poulet-lab/Bpod_Stepper/PCB/bpod_stepper_1.3.1.brd

## EAGLE design PCB/bpod_stepper_1.3.1.brd (2021-09-14)

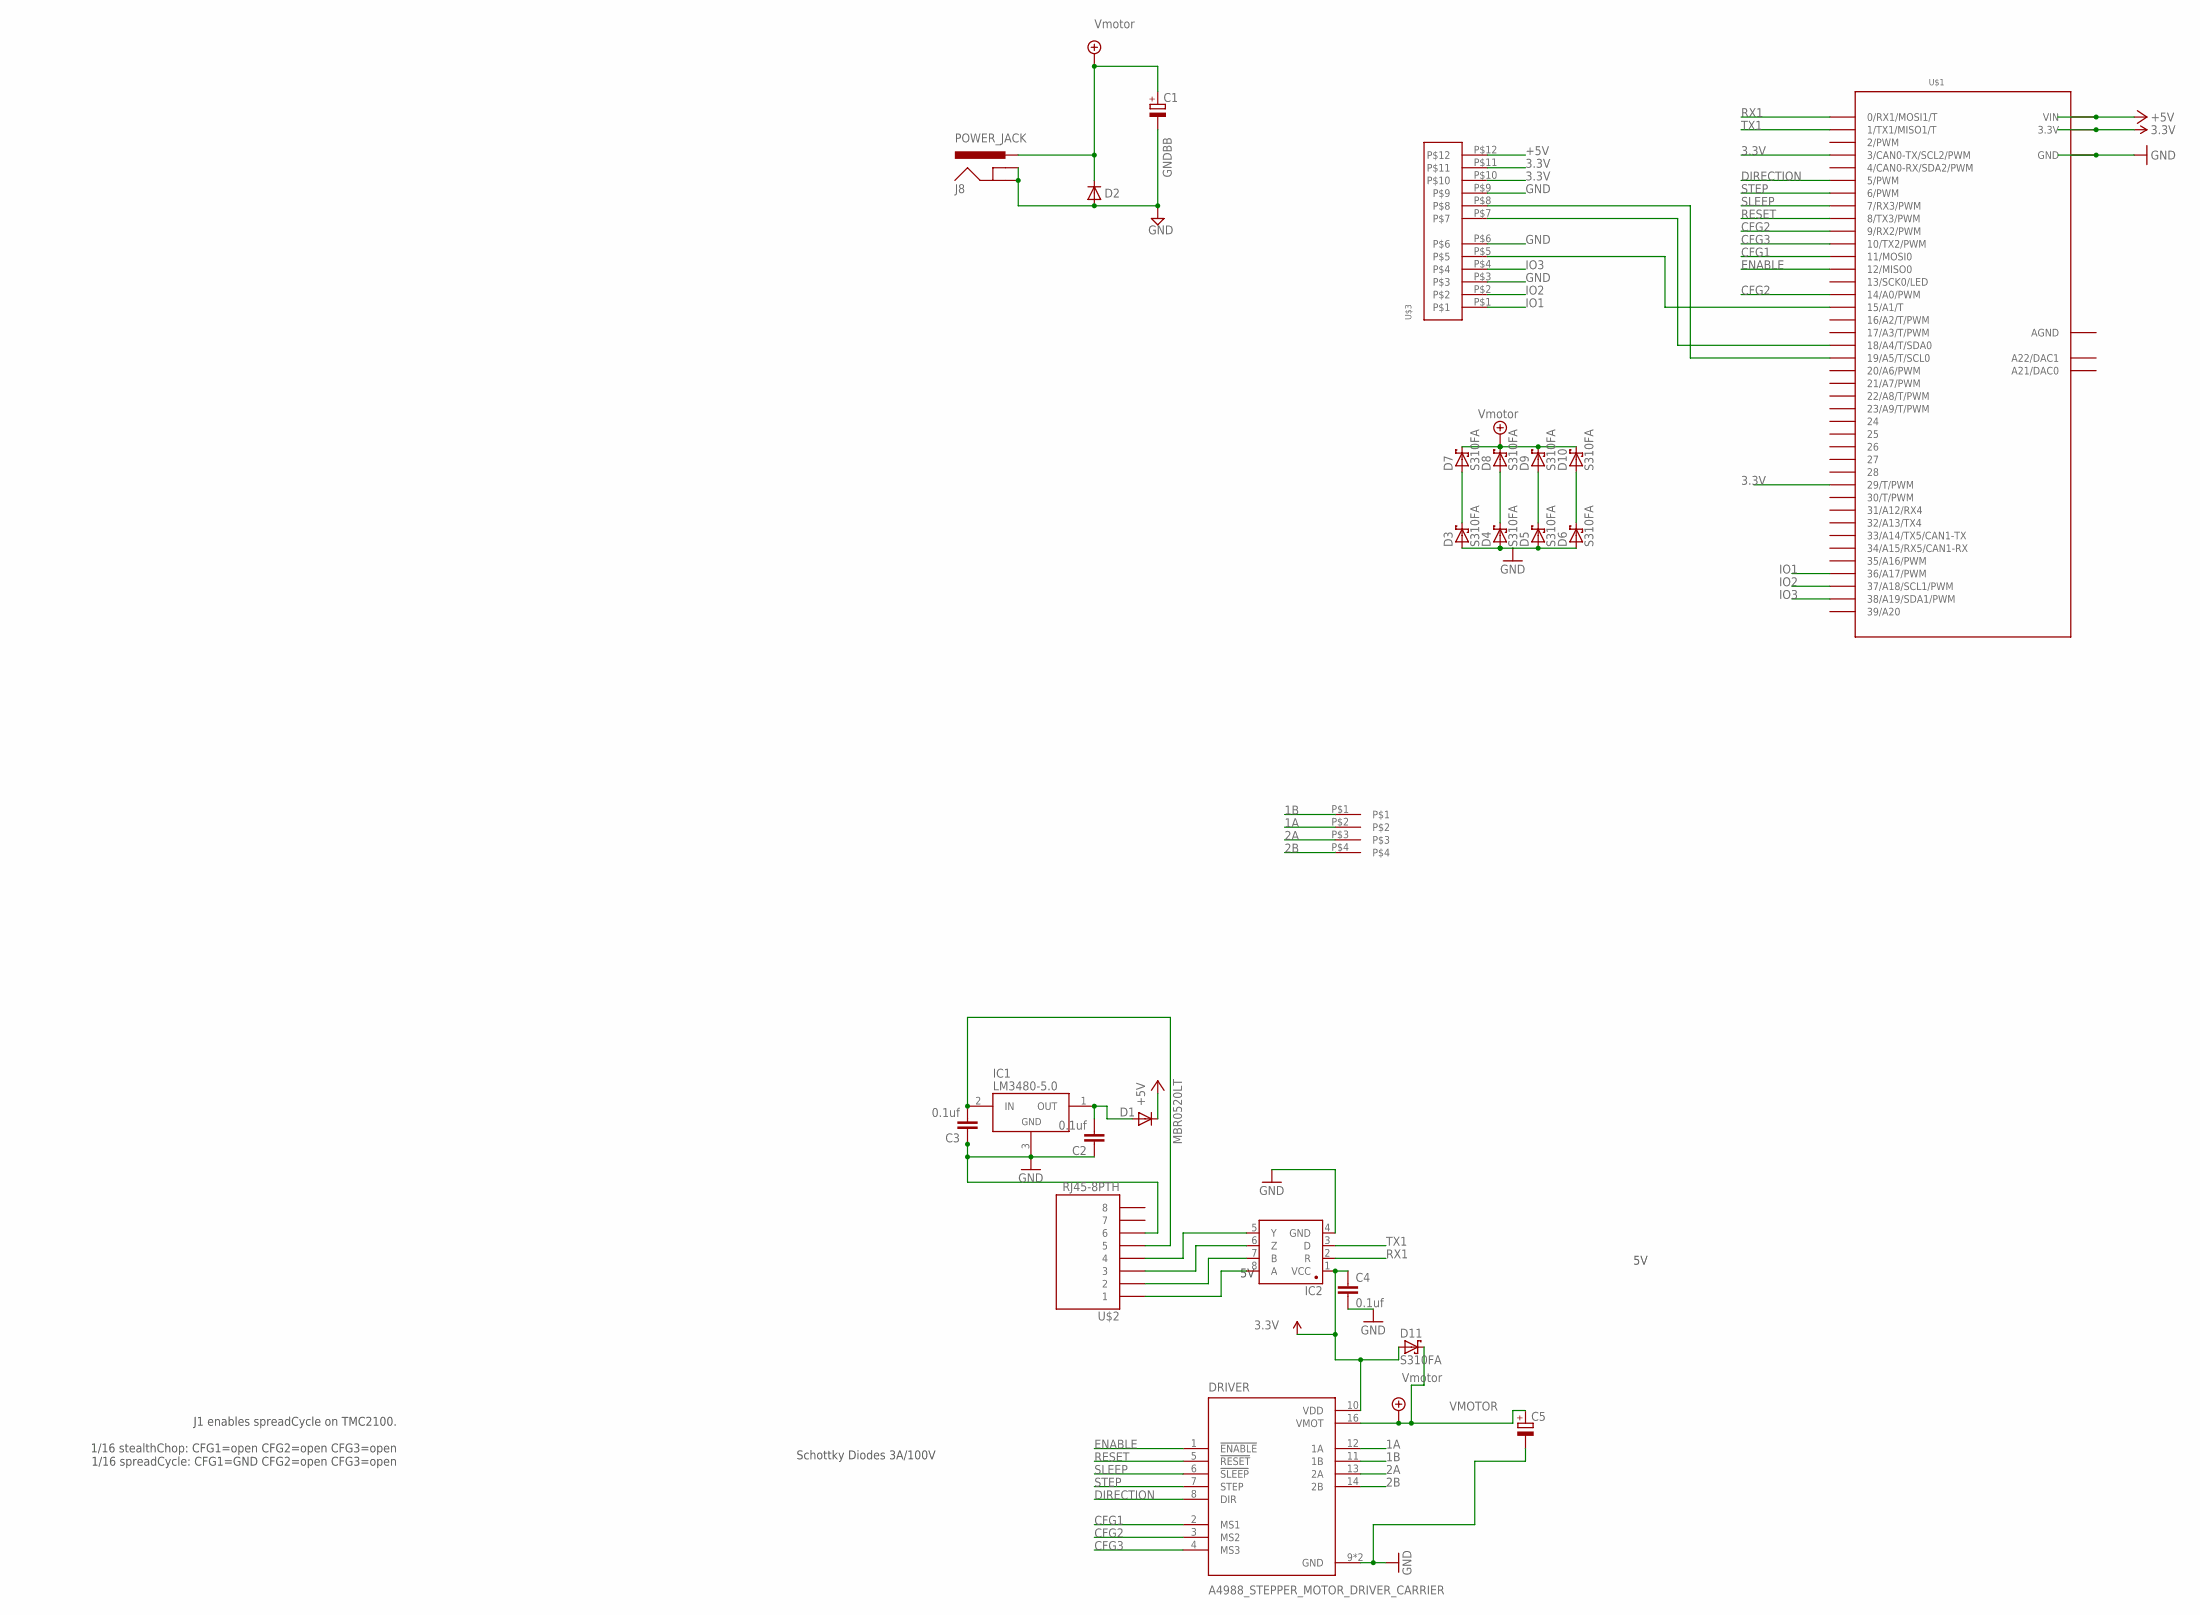
[picture p7: schematic bpod_stepper_1.3.1.sch]

Parts:
C1, C5: CPOL-EUG; PANASONIC_G
C2, C3, C4: 0.1uf; 1206@1
D1: MBR0520LT; SOD123
D2: DIODE-DO214AA; DO214AA
D3, D4, D5, D6, D7, D8, D9, D10, D11: S310FA; SOD123
DRIVER: A4988_STEPPER_MOTOR_DRIVER_CARRIER; MODULE_A4988_STEPPER_MOTOR_DRIVER_CARRIER
IC1: LM3480-5.0; SOT-23-3
IC2: SN65HVD31DR; SO08
J8: POWER_JACK; POWER_JACK_PTH
U$1: TEENSY_3.6_DIL
U$2: RJ45-8PTH; RJ45-8
U$3: 12POS_MOLEX_SOCKET
U$4: MOLEX395221004

Connections:
1A: D4.C, D8.A, DRIVER.12 (1A), U$4.P$2
1B: D3.C, D7.A, DRIVER.11 (1B), U$4.P$1
2A: D6.C, D10.A, DRIVER.13 (2A), U$4.P$3
2B: D5.C, D9.A, DRIVER.14 (2B), U$4.P$4
3.3V: C4.1, D11.A, DRIVER.10 (VDD), IC2.1 (VCC), U$1.3 (3/CAN0-TX/SCL2/PWM), U$1.3.3V, U$1.3.3V3 (3.3V), U$1.29 (29/T/PWM), U$3.P$10, U$3.P$11
+5V: D1.C, U$1.VIN, U$3.P$12
AGND: U$1.AGND
CFG1: DRIVER.2 (MS1), U$1.11 (11/MOSI0)
CFG2: DRIVER.3 (MS2), U$1.9 (9/RX2/PWM), U$1.14/A0 (14/A0/PWM)
CFG3: DRIVER.4 (MS3), U$1.10 (10/TX2/PWM)
DIRECTION: DRIVER.8 (DIR), U$1.5 (5/PWM)
ENABLE: DRIVER.1 (!ENABLE), U$1.12 (12/MISO0)
GND: C1.-, C2.1, C3.1, C4.2, C5.-, D2.A, D3.A, D4.A, D5.A, D6.A, DRIVER.9 (GND), DRIVER.15 (GND), IC1.3 (GND), IC2.4 (GND), J8.GND, J8.GNDBREAK, U$1.GND, U$1.GND1 (GND), U$2.6, U$3.P$3, U$3.P$6, U$3.P$9
IO1: U$1.36/A17 (36/A17/PWM), U$3.P$1
IO2: U$1.37/A18 (37/A18/SCL1/PWM), U$3.P$2
IO3: U$1.38/A19 (38/A19/SDA1/PWM), U$3.P$4
unnamed: U$1.19/A5 (19/A5/T/SCL0), U$3.P$8
unnamed: U$1.18/A4 (18/A4/T/SDA0), U$3.P$7
unnamed: U$1.15/A1 (15/A1/T), U$3.P$5
unnamed: IC2.8 (A), U$2.1
unnamed: IC2.7 (B), U$2.2
unnamed: IC2.6 (Z), U$2.3
unnamed: IC2.5 (Y), U$2.4
unnamed: C2.2, D1.A, IC1.1 (OUT)
unnamed: C3.2, IC1.2 (IN), U$2.5
RESET: DRIVER.5 (!RESET), U$1.8 (8/TX3/PWM)
RX1: IC2.2 (R), U$1.0 (0/RX1/MOSI1/T)
SLEEP: DRIVER.6 (!SLEEP), U$1.7 (7/RX3/PWM)
STEP: DRIVER.7 (STEP), U$1.6 (6/PWM)
TX1: IC2.3 (D), U$1.1 (1/TX1/MISO1/T)
VMOTOR: C1.+, C5.+, D2.C, D7.C, D8.C, D9.C, D10.C, D11.C, DRIVER.16 (VMOT), J8.PWR

Notes on the sheet:
GNDBB
Schottky Diodes 3A/100V
J1 enables spreadCycle on TMC2100. 1/16 stealthChop: CFG1=open CFG2=open CFG3=open 1/16 spreadCycle: CFG1=GND CFG2=open CFG3=open

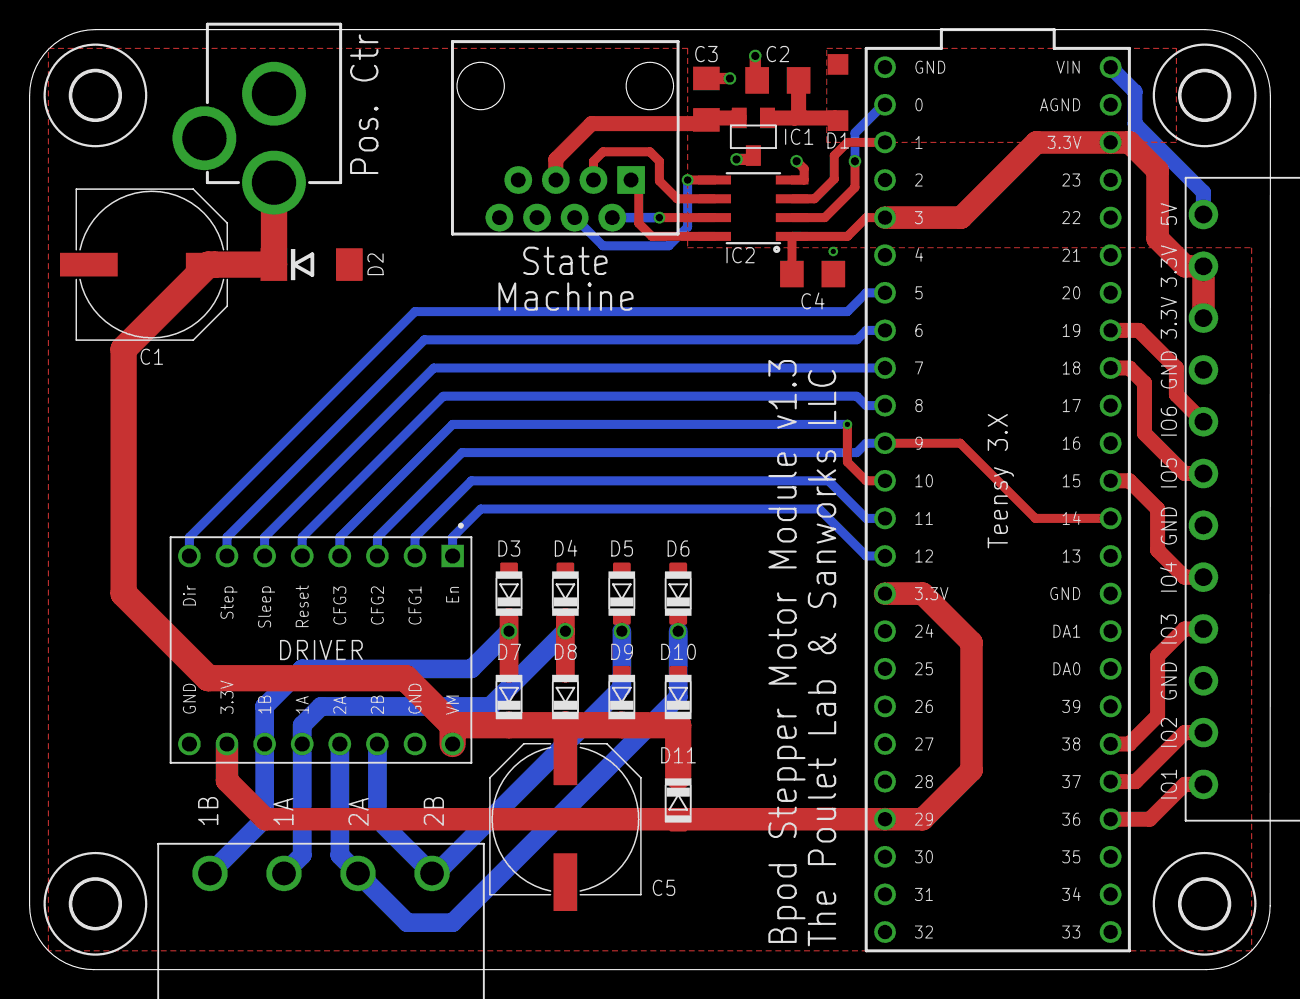
[picture p8: board bpod_stepper_1.3.1.brd from above]

Board: 2 copper layers, 83.8 x 63.5 mm, 28 parts (0 on the bottom side), 30 nets.

Other parts of the board:
U$7, U$8, U$9, U$10: 3,2
