poulet-lab/Bpod_Stepper/PCB/bpod_stepper_1.0.brd

## EAGLE design PCB/bpod_stepper_1.0.brd (2020-08-25)

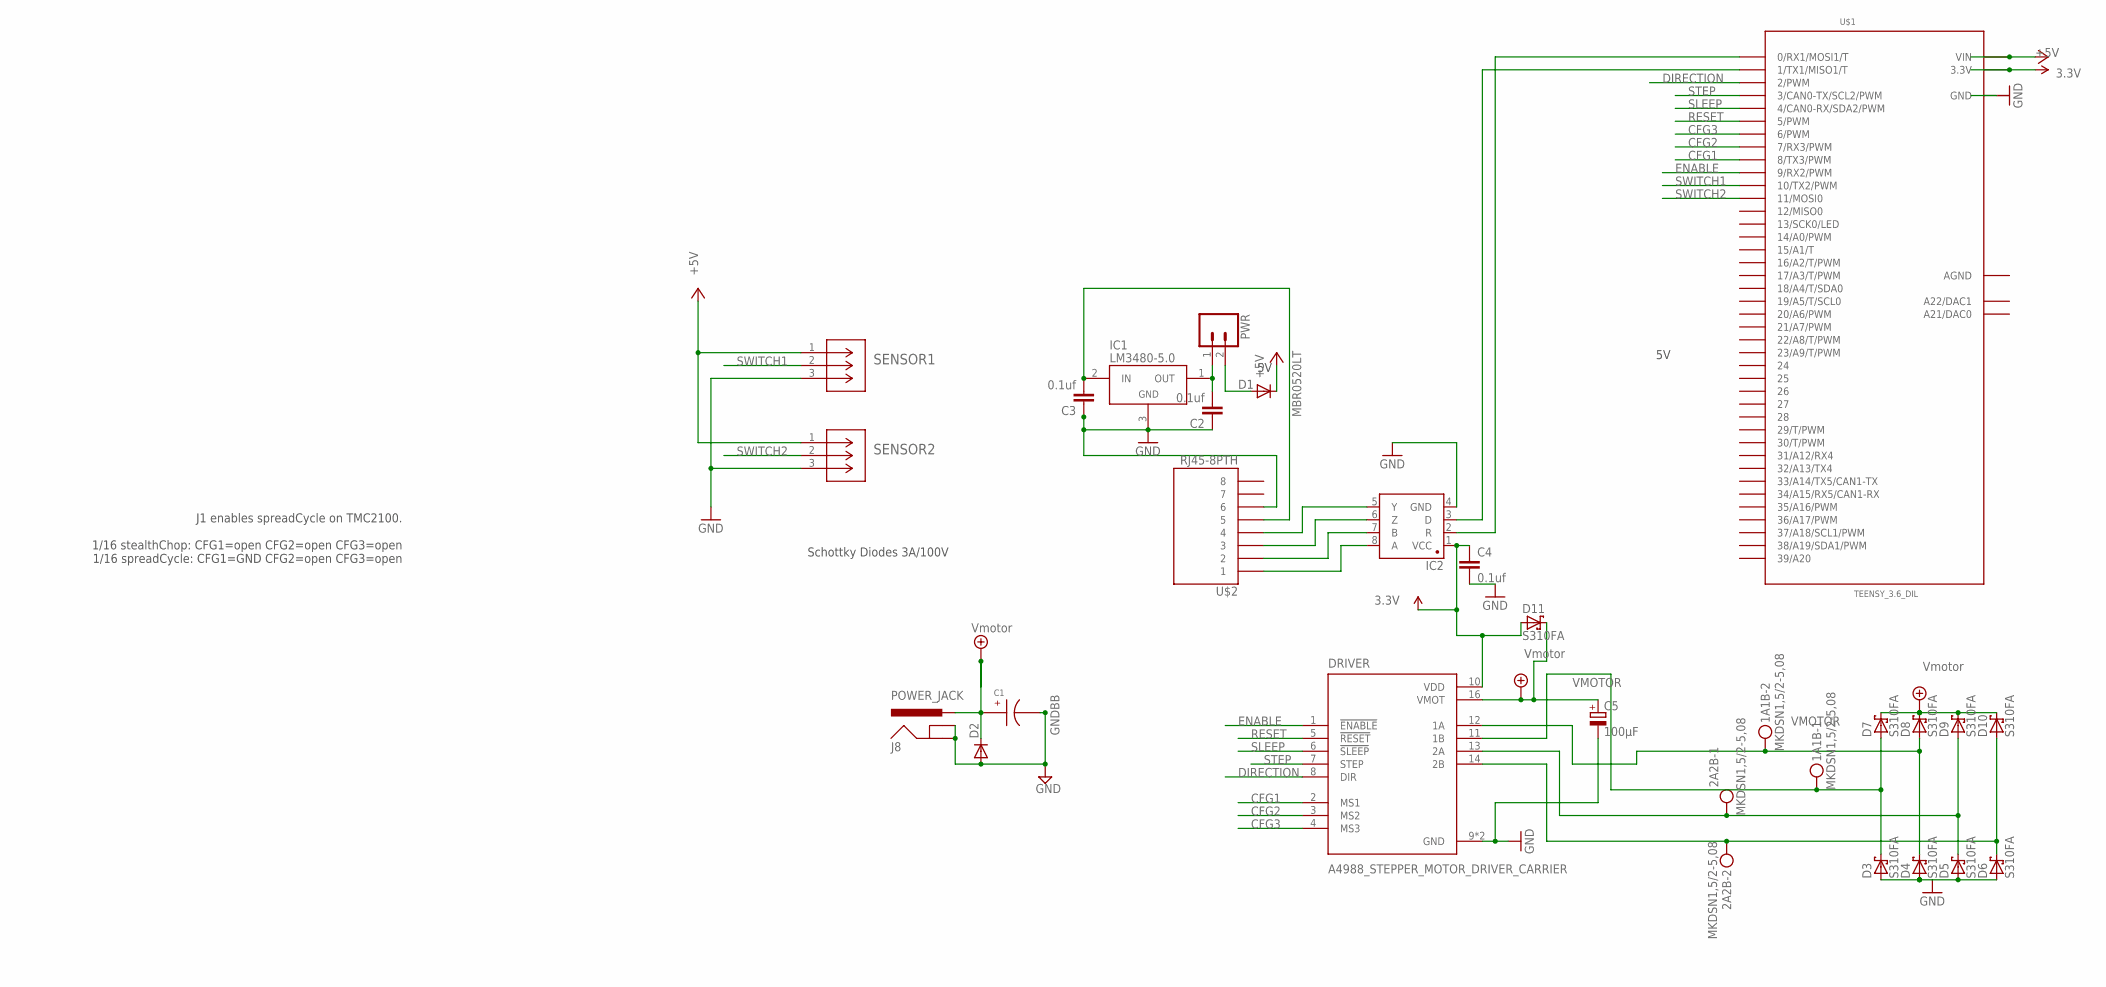
[picture p9: schematic bpod_stepper_1.0.sch]

Parts:
1A1B, 2A2B: MKDSN1,5/2-5,08
C1: EEE-FK1H100UR
C2, C3, C4: 0.1uf; 1206@1
C5: 100µF; E2,5-6E
D1: MBR0520LT; SOD123
D2: DIODE-DO214AA; DO214AA
D3, D4, D5, D6, D7, D8, D9, D10, D11: S310FA; SOD123
DRIVER: A4988_STEPPER_MOTOR_DRIVER_CARRIER; MODULE_A4988_STEPPER_MOTOR_DRIVER_CARRIER
IC1: LM3480-5.0; SOT-23-3
IC2: SN65HVD31DR; SO08
J8: POWER_JACK; POWER_JACK_PTH
PWR: CONN_02; 1X02
SENSOR1, SENSOR2: 282834-3; CONN_282834-3_TYC
U$1: TEENSY_3.6_DIL
U$2: RJ45-8PTH; RJ45-8

Connections:
3.3V: C4.1, D11.A, DRIVER.10 (VDD), IC2.1 (VCC), U$1.3.3V, U$1.3.3V3 (3.3V)
+5V: D1.C, SENSOR1.1, SENSOR2.1, U$1.VIN
AGND: U$1.AGND
CFG1: DRIVER.2 (MS1), U$1.8 (8/TX3/PWM)
CFG2: DRIVER.3 (MS2), U$1.7 (7/RX3/PWM)
CFG3: DRIVER.4 (MS3), U$1.6 (6/PWM)
DIRECTION: DRIVER.8 (DIR), U$1.2 (2/PWM)
ENABLE: DRIVER.1 (!ENABLE), U$1.9 (9/RX2/PWM)
GND: C1.CATHODE, C2.1, C3.1, C4.2, C5.-, D2.A, D3.A, D4.A, D5.A, D6.A, DRIVER.9 (GND), DRIVER.15 (GND), IC1.3 (GND), IC2.4 (GND), J8.GND, J8.GNDBREAK, SENSOR1.3, SENSOR2.3, U$1.GND, U$1.GND1 (GND), U$2.6
M1A1: 1A1B.1, D3.C, D7.A, DRIVER.11 (1B)
M1B1: 1A1B.2, D4.C, D8.A, DRIVER.12 (1A)
M2A1: 2A2B.1, D5.C, D9.A, DRIVER.13 (2A)
M2B1: 2A2B.2, D6.C, D10.A, DRIVER.14 (2B)
unnamed: IC2.8 (A), U$2.1
unnamed: IC2.7 (B), U$2.2
unnamed: IC2.6 (Z), U$2.3
unnamed: IC2.5 (Y), U$2.4
unnamed: C2.2, IC1.1 (OUT), PWR.1
unnamed: D1.A, PWR.2
unnamed: C3.2, IC1.2 (IN), U$2.5
RESET: DRIVER.5 (!RESET), U$1.5 (5/PWM)
RX1: IC2.2 (R), U$1.0 (0/RX1/MOSI1/T)
SLEEP: DRIVER.6 (!SLEEP), U$1.4 (4/CAN0-RX/SDA2/PWM)
STEP: DRIVER.7 (STEP), U$1.3 (3/CAN0-TX/SCL2/PWM)
SWITCH1: SENSOR1.2, U$1.10 (10/TX2/PWM)
SWITCH2: SENSOR2.2, U$1.11 (11/MOSI0)
TX1: IC2.3 (D), U$1.1 (1/TX1/MISO1/T)
VMOTOR: C1.ANODE, C5.+, D2.C, D7.C, D8.C, D9.C, D10.C, D11.C, DRIVER.16 (VMOT), J8.PWR

Notes on the sheet:
GNDBB
Schottky Diodes 3A/100V
J1 enables spreadCycle on TMC2100. 1/16 stealthChop: CFG1=open CFG2=open CFG3=open 1/16 spreadCycle: CFG1=GND CFG2=open CFG3=open

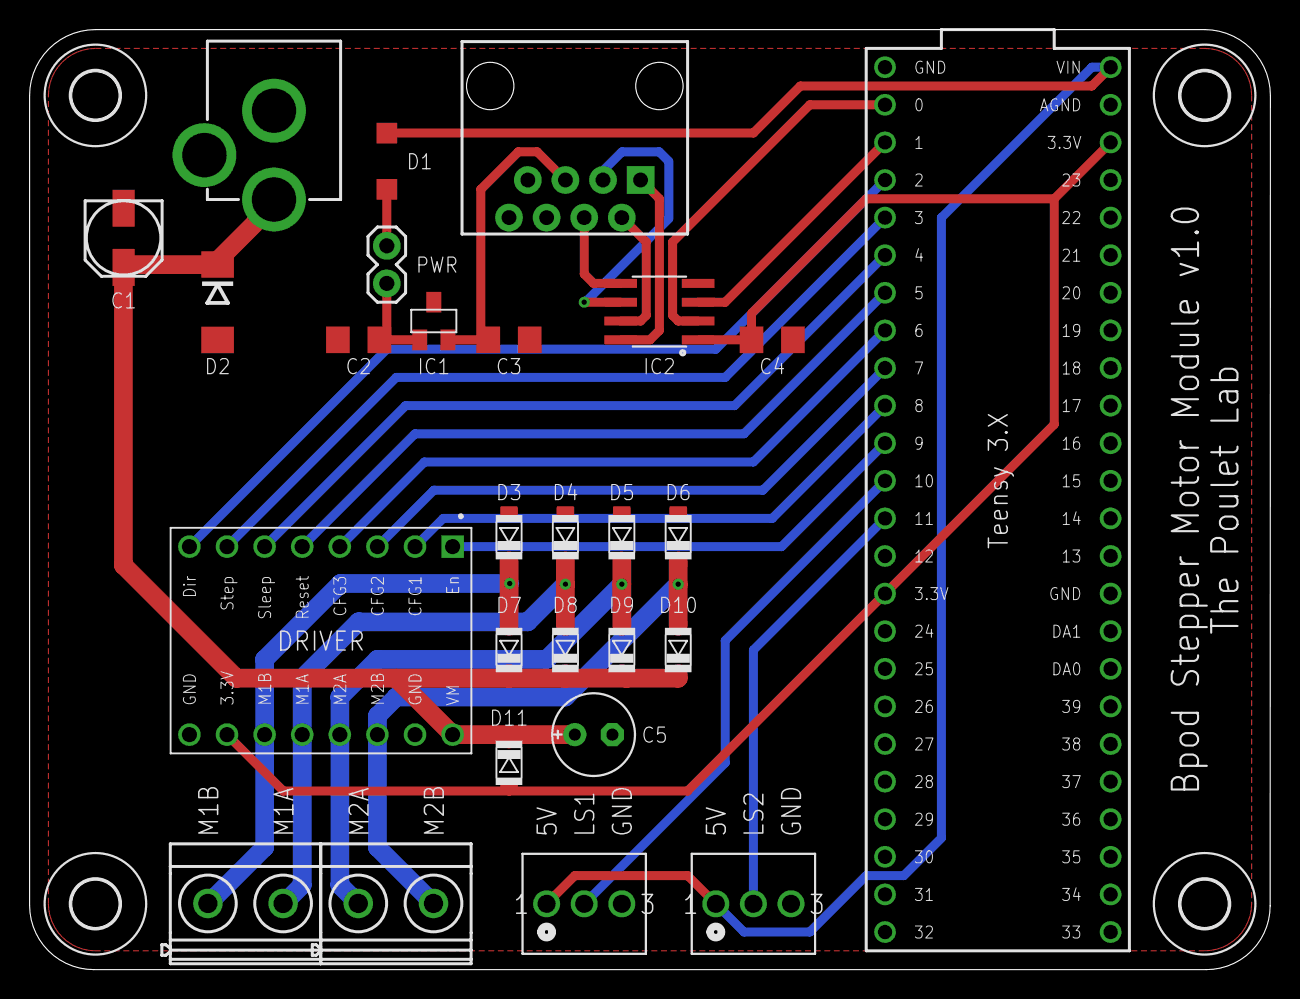
[picture p10: board bpod_stepper_1.0.brd from above]

Board: 2 copper layers, 83.8 x 63.5 mm, 31 parts (0 on the bottom side), 27 nets.

Other parts of the board:
U$7, U$8, U$9, U$10: 3,2
