poulet-lab/Bpod_Stepper/firmware/src/StepperWrapper_MotionControl.cpp

/*
StepperWrapper
Copyright (C) 2023 Florian Rau

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

_______________________________________________________________________________
*/

#include <Arduino.h>
#include <TMCStepper.h>
#include "StepperWrapper.h"
#include "SerialDebug.h"

StepperWrapper_MotionControl::StepperWrapper_MotionControl()
    : StepperWrapper() {}

void StepperWrapper_MotionControl::init() {
  StepperWrapper::init();

  // if (PCBrev < 1.4)
  // throwError(42);
}

float StepperWrapper_MotionControl::a() {
  DEBUG_PRINTFUN();
  return TMC5160->AMAX() / factA / _microsteps;
}

void StepperWrapper_MotionControl::a(float aHzs) {
  DEBUG_PRINTFUN(aHzs);
  // a5160 = aHzs / fCLK^2 / (512*256) / 2^24
  uint16_t a5160 =
      round(constrain(aHzs * factA * _microsteps, 0, uint16_t(-1)));
  TMC5160->AMAX(a5160);
  TMC5160->DMAX(a5160);
  TMC5160->a1(a5160);
  TMC5160->d1(a5160);
}

void StepperWrapper_MotionControl::hardStop() {
  DEBUG_PRINTFUN();
  // TODO
}

void StepperWrapper_MotionControl::moveMicroSteps(int32_t steps) {
  DEBUG_PRINTFUN(steps);
  TMC5160->XTARGET(TMC5160->XACTUAL() + steps);
}

int32_t StepperWrapper_MotionControl::microPosition() {
  DEBUG_PRINTFUN();
  return TMC5160->XACTUAL();
}

void StepperWrapper_MotionControl::microPosition(int32_t target) {
  DEBUG_PRINTFUN(target);
  TMC5160->RAMPMODE(0);
  TMC5160->XTARGET(target);
}

void StepperWrapper_MotionControl::setPosition(int32_t pos) {
  DEBUG_PRINTFUN();
  TMC5160->RAMPMODE(3);
  TMC5160->XACTUAL(pos);
}

void StepperWrapper_MotionControl::rotate(int8_t direction) {
  DEBUG_PRINTFUN();
  // TODO
}

void StepperWrapper_MotionControl::softStop() {
  DEBUG_PRINTFUN();
  // TODO
}

float StepperWrapper_MotionControl::vMax() {
  DEBUG_PRINTFUN();
  return TMC5160->VMAX() / factV / _microsteps;
}

void StepperWrapper_MotionControl::vMax(float vHz) {
  DEBUG_PRINTFUN(vHz);
  // v5160 = vHz / ( fCLK/2 / 2^23 )
  uint32_t v5160 =
      round(constrain(vHz * factV * _microsteps, 0, pow(2, 23) - 512));
  TMC5160->VMAX(v5160);
  TMC5160->v1(0); // Disables A1 and D1 phase, use AMAX, DMAX only
}

bool StepperWrapper_MotionControl::isRunning() { return TMC5160->stst(); }
